jgw4/doppel-1/doc/a1man-latex/pages/a1man_pages-12.png

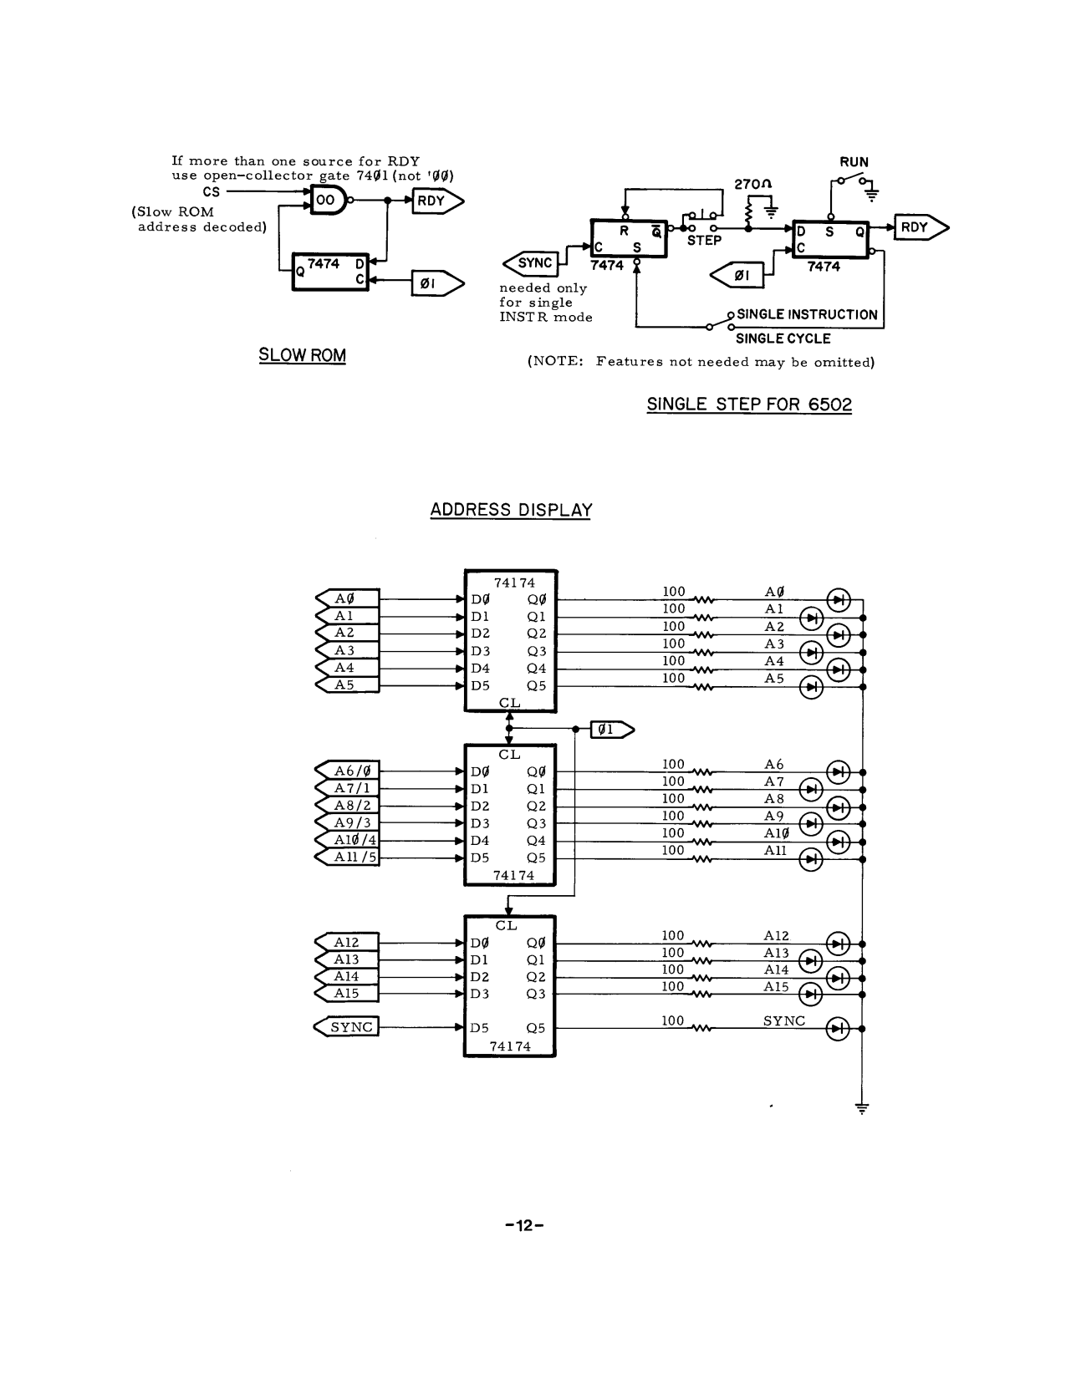
doc/a1man-latex/pages/a1man_pages-12.png
