jgw4/doppel-1/doc/a1man-latex/pages/a1man_pages-14.png

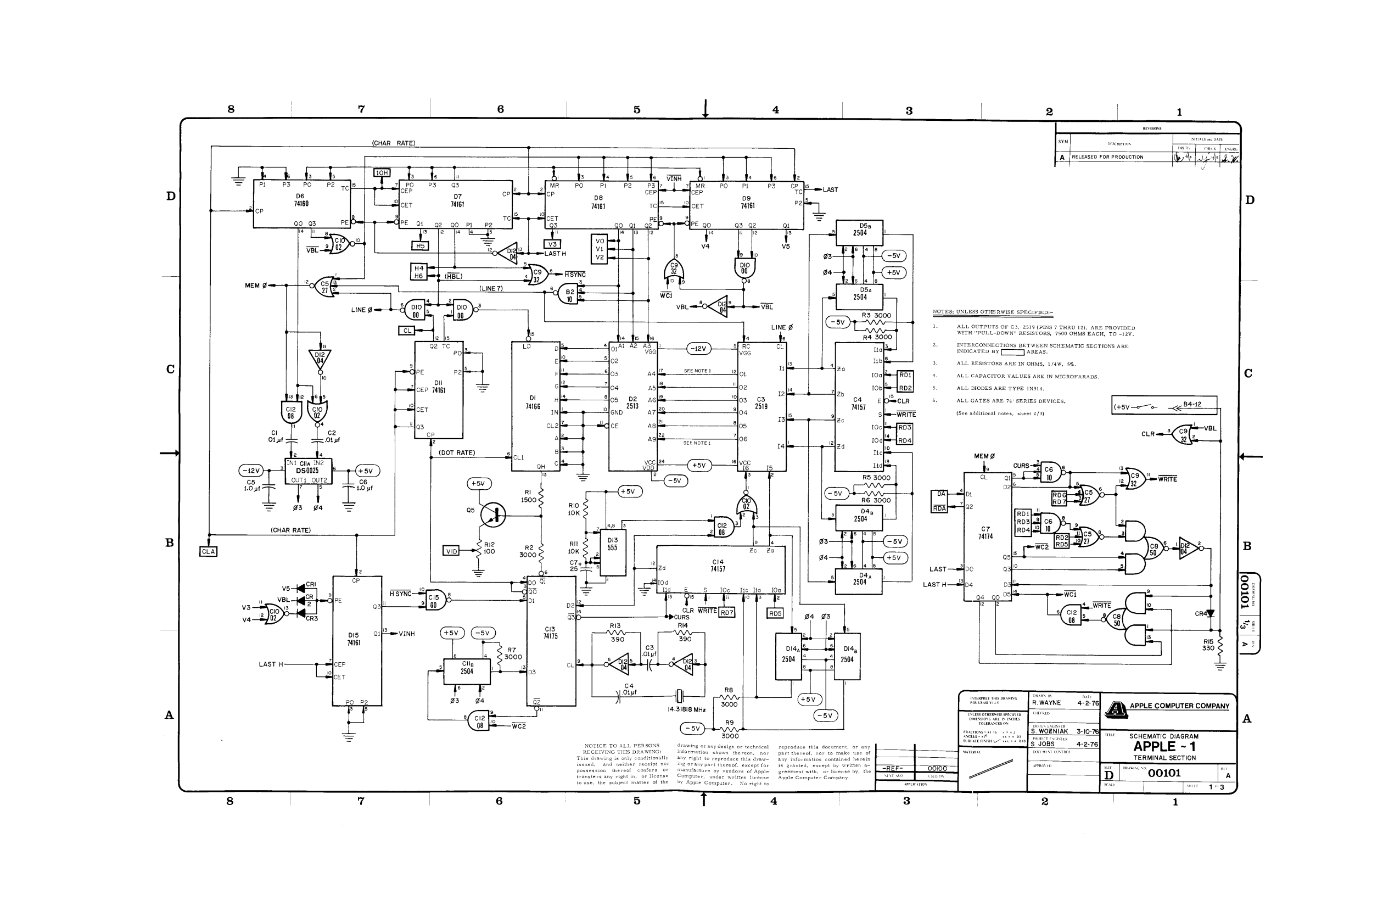
doc/a1man-latex/pages/a1man_pages-14.png
