jgw4/doppel-1/doc/a1man-latex/pages/sch_terminal.png

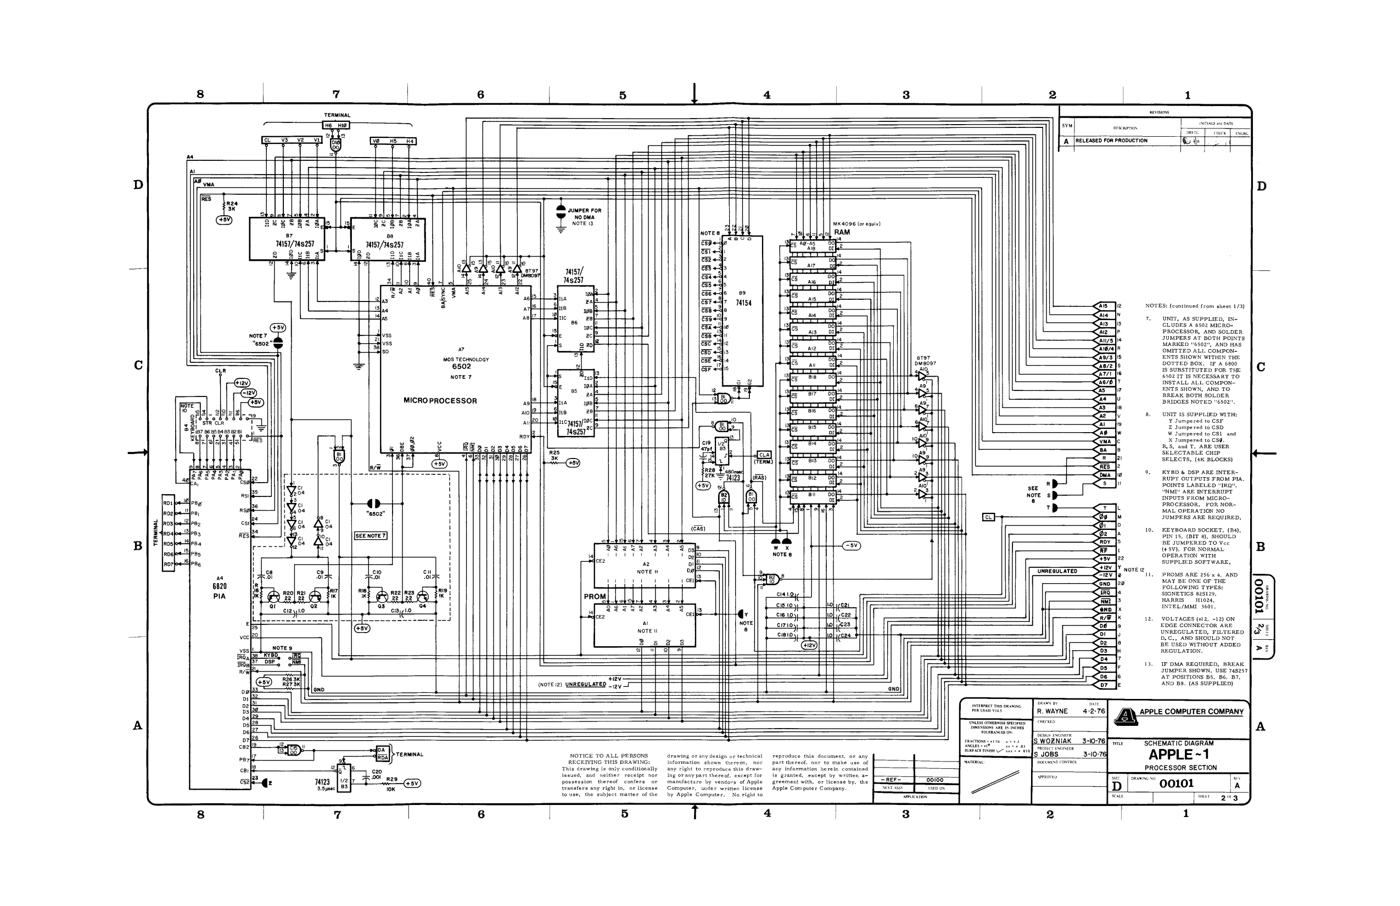
doc/a1man-latex/pages/sch_terminal.png
