jgw4/doppel-1/img/15b2.jpg

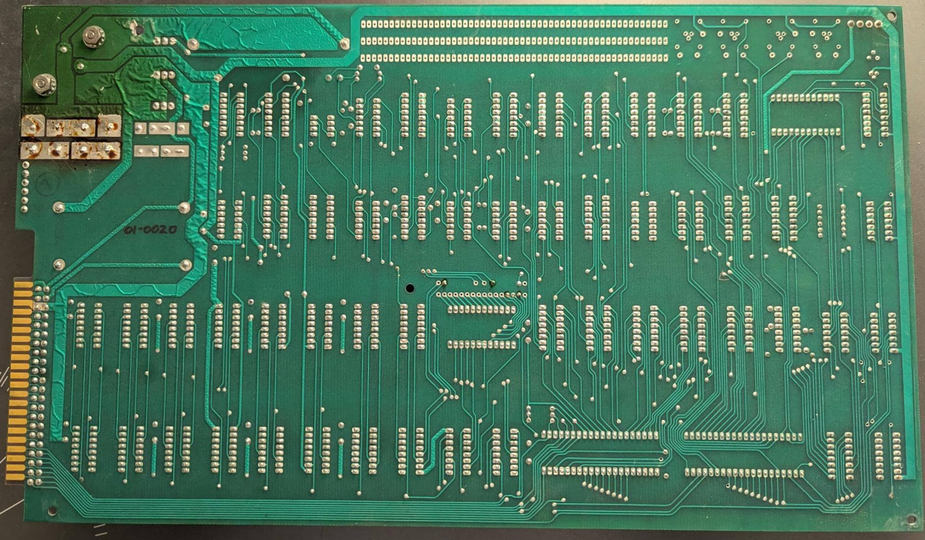
img/15b2.jpg
