jgw4/doppel-1/img/15b2_corrected.jpg

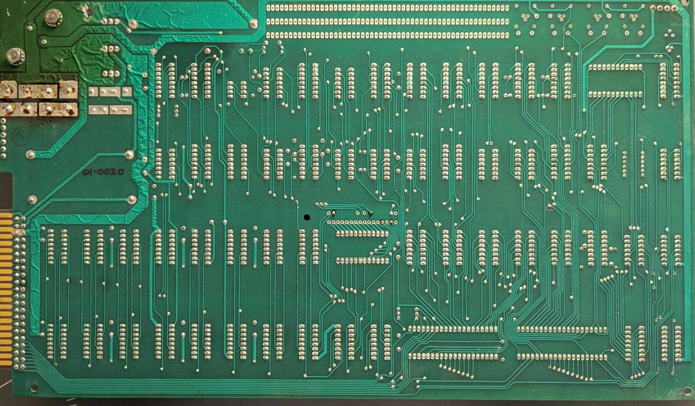
img/15b2_corrected.jpg
