jgw4/doppel-1/img/a1-cad - Copy.jpg

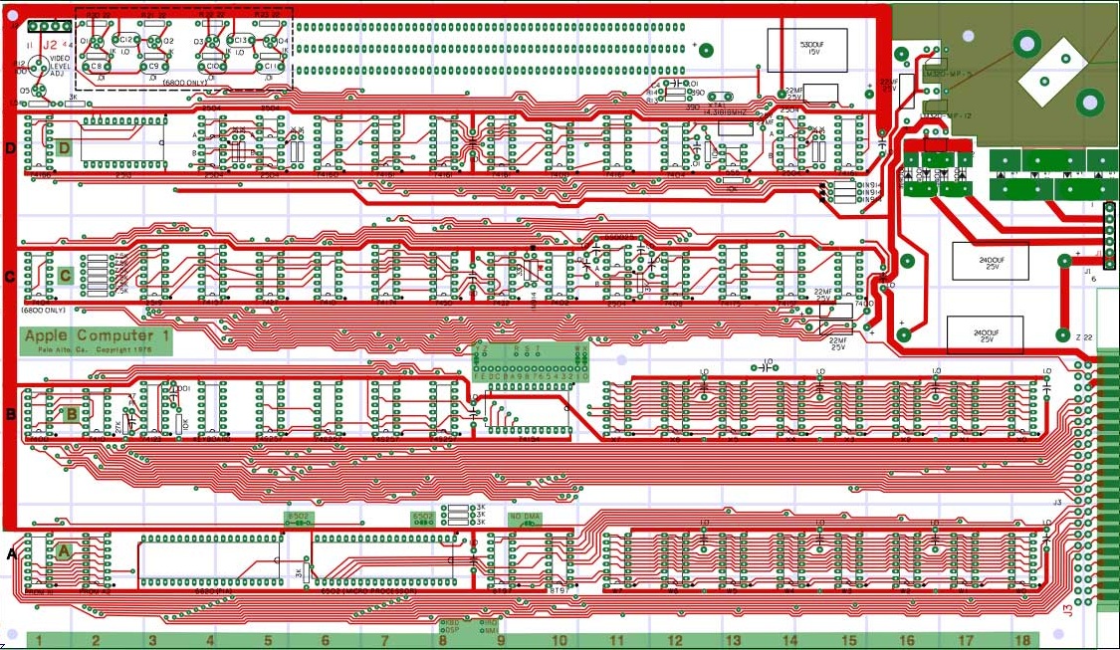
img/a1-cad - Copy.jpg
