jgw4/doppel-1/img/a1replica-back.jpg

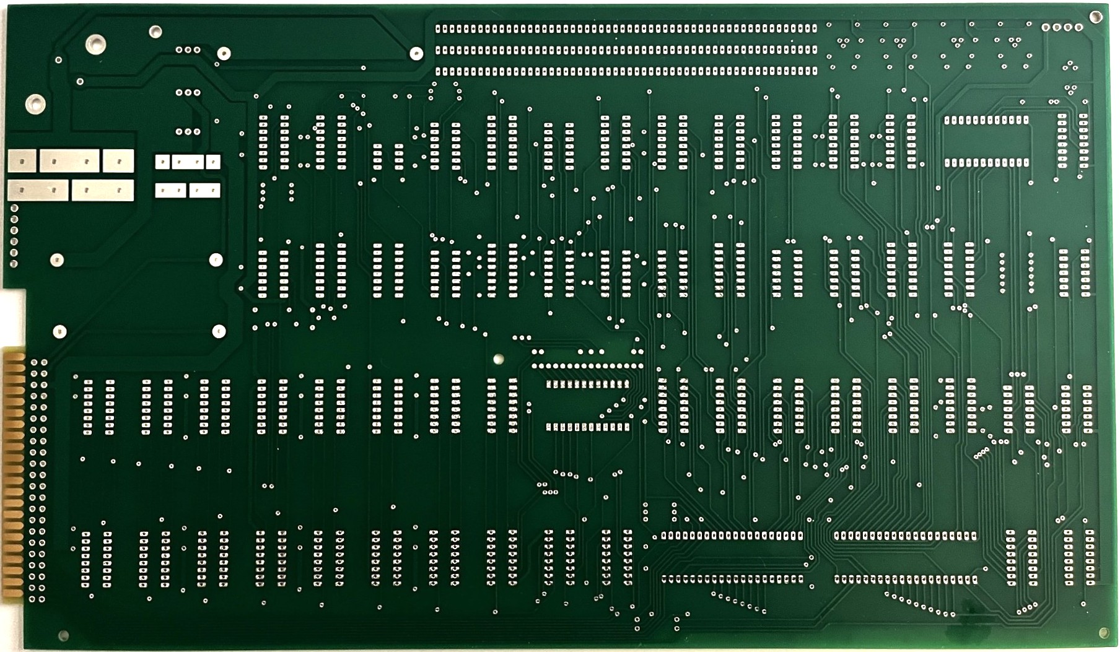
img/a1replica-back.jpg
