jgw4/doppel-1/img/apple-1-board.jpg

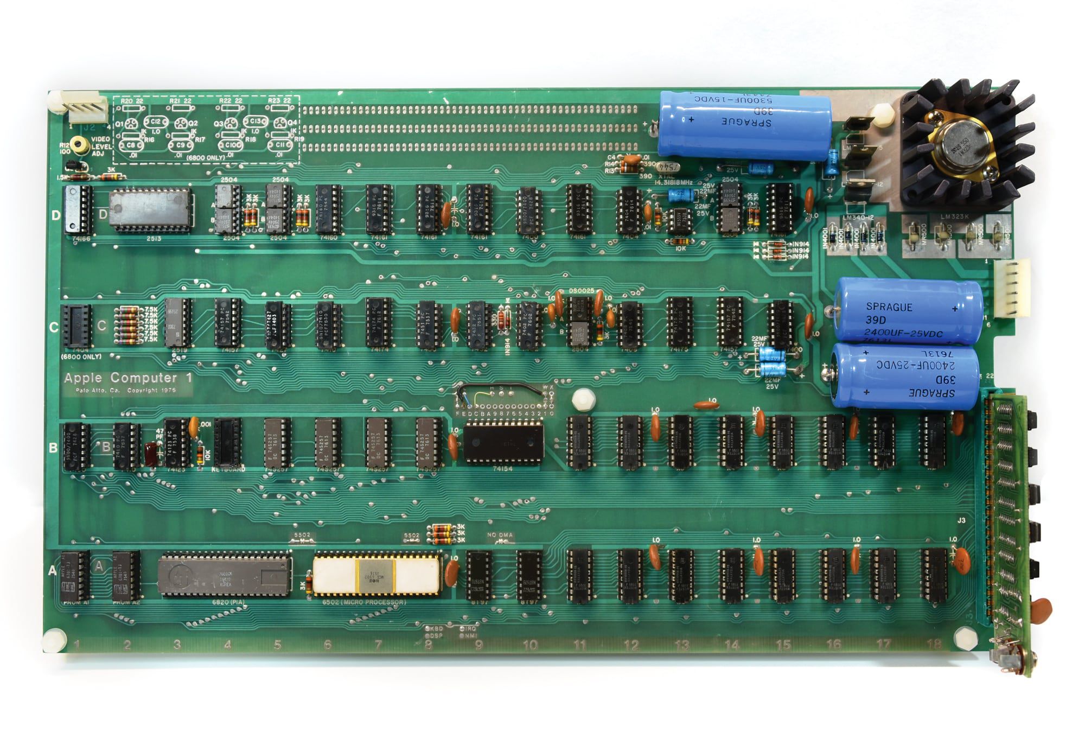
img/apple-1-board.jpg
