jgw4/doppel-1/d1.step

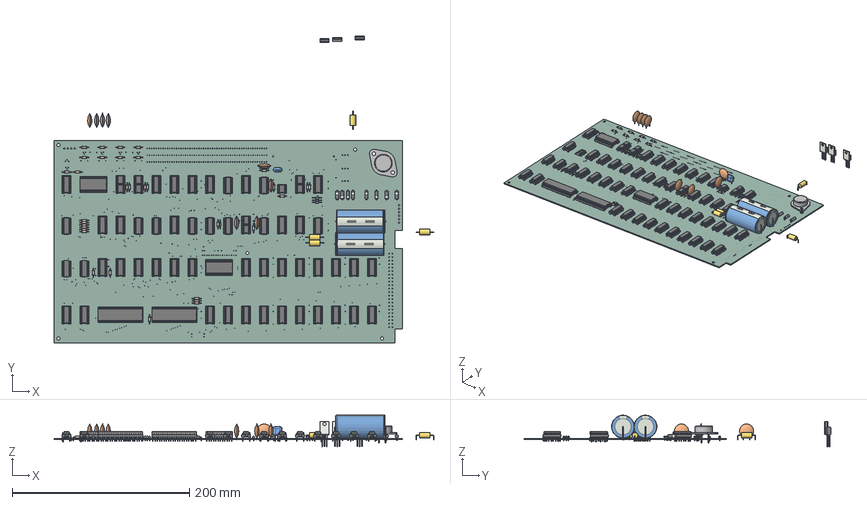
[picture p22: CAD file, 2026-09-14]
d1.step
429.3 x 346.7 x 35.8 mm
DIP_14_W762mm_Socket x 12
DIP-14_W7.62mm x 12
DIP_16_W762mm_Socket x 38
DIP-16_W7.62mm x 38
R_Axial_DIN0207_L63mm_D25mm_P1016mm_Horizontal x 34
D_DO-35_SOD27_P10.16mm_Horizontal x 4
C_Disc_D160mm_W50mm_P750mm x 8
D_5W_P10.16mm_Horizontal x 8
DIP_8_W762mm_Socket x 9
DIP-8_W7.62mm x 9
C_Axial_L120mm_D65mm_P2000mm_Horizontal x 4
Resonator-2pin_w10.0mm_h5.0mm
CP_Axial_L54.4mm_D26.0mm_P55.88mm_Horizontal x 2
TO-220-3_Vertical x 3
TO-3
DIP_40_W1524mm_Socket x 2
DIP-40_W15.24mm x 2
DIP_24_W1524mm_Socket x 2
DIP_24_W1524mm x 2
mainboard_PCB
